Arctic-Techworks/MEH01/img/bearings_zzr.jpeg

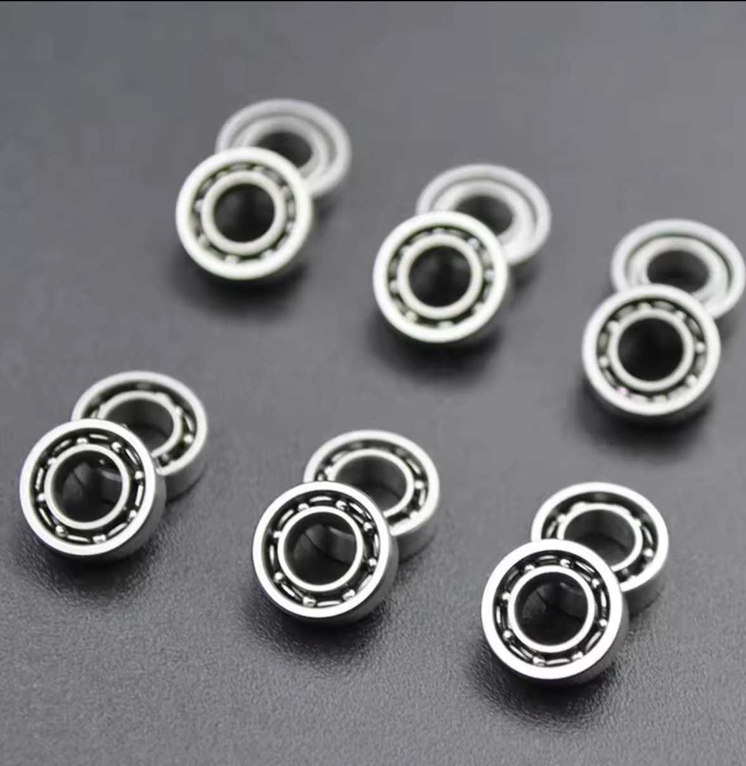
img/bearings_zzr.jpeg
