Arctic-Techworks/MEH01/img/metal_pin_1.jpg

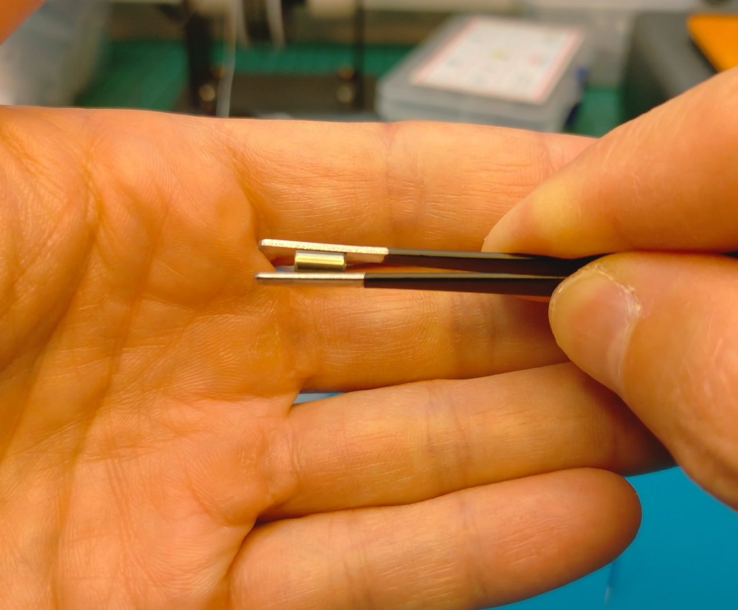
img/metal_pin_1.jpg
