Arctic-Techworks/MEH01/img/metal_pin_2.jpg

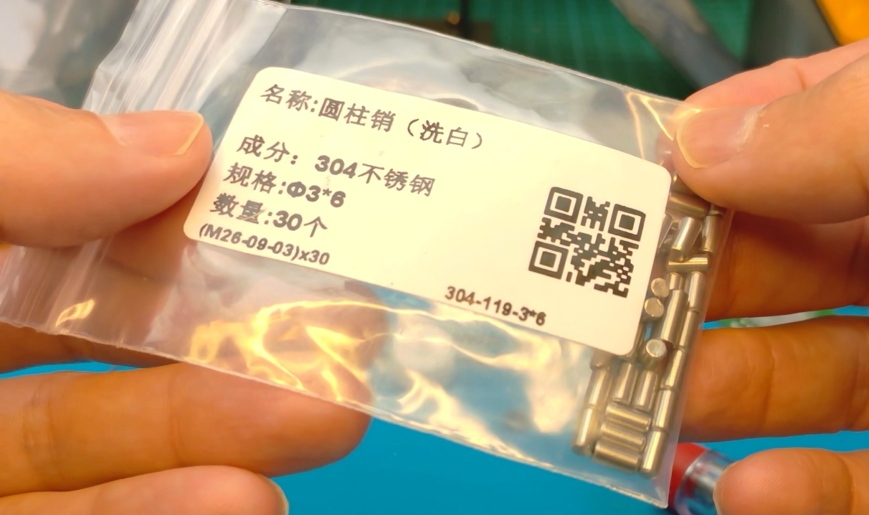
img/metal_pin_2.jpg
