Arctic-Techworks/MEH01/img/wire_awg_30_1.jpg

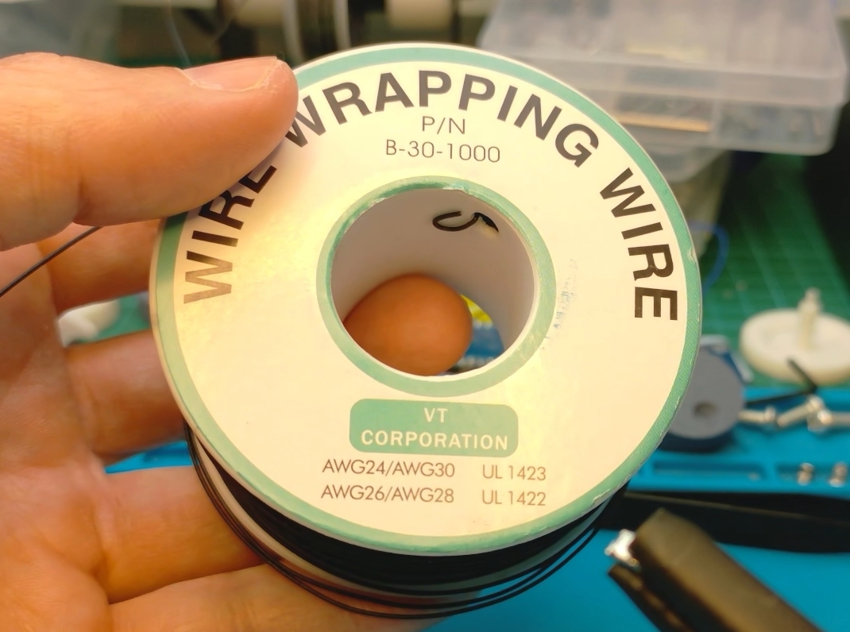
img/wire_awg_30_1.jpg
